Jajcus/midi_touch_keyboard/src/touch_sensors.rs

use defmt::{debug, info, write, Format, Formatter};

use embassy_rp::gpio::{Flex, Pull};
use embassy_time::{Duration, Instant, Timer};

use crate::config::*;

#[derive(Default, Clone, Copy, Format, PartialEq)]
pub enum CalibrationStatus {
    #[default]
    NA,
    Ok,
    Bad,
}

#[derive(Clone, Copy)]
pub struct CalibrationData {
    pub min_time: Duration,
    pub max_time: Duration,
    pub status: CalibrationStatus,
}

impl Default for CalibrationData {
    fn default() -> Self {
        Self {
            min_time: Duration::MAX,
            max_time: Duration::MIN,
            status: CalibrationStatus::NA,
        }
    }
}

#[derive(Default, Clone, Copy)]
pub struct CalibrationDataSet {
    pub pins: [CalibrationData; NUM_SENSORS],
    pub all: CalibrationData,
    pub status: CalibrationStatus,
}

impl Format for CalibrationDataSet {
    fn format(&self, f: Formatter) {
        write!(f, "{}: ", self.status);
        let mut first = true;
        for pin_data in self.pins {
            if !first {
                write!(f, ", ");
            } else {
                first = false;
            }
            write!(f, "{}[", pin_data.status);
            if pin_data.min_time < Duration::MAX {
                write!(f, "{}", pin_data.min_time.as_micros());
            }
            write!(f, "..");
            if pin_data.max_time > Duration::MIN {
                write!(f, "{}", pin_data.max_time.as_micros());
            }
            write!(f, "]");
        }
    }
}

#[derive(Default, Clone, Copy, Format, PartialEq)]
pub enum TouchSensorStatus {
    #[default]
    NA,
    On,
    Off,
}

pub struct TouchSensors<'a> {
    pins: [Flex<'a>; NUM_SENSORS],
    calibration: CalibrationDataSet,
    threshold: Duration,
}

impl<'a> TouchSensors<'a> {
    pub fn new(mut pins: [Flex<'a>; NUM_SENSORS]) -> Self {
        let threshold = Duration::from_micros(500);

        for pin in &mut pins {
            pin.set_pull(Pull::None);
        }

        Self {
            pins,
            calibration: Default::default(),
            threshold,
        }
    }
    pub async fn calibrate_start(&mut self) {
        info!("Calibration start");
        self.calibration = Default::default();
    }
    pub async fn calibrate_step(&mut self) -> CalibrationDataSet {
        info!("Calibration step");

        for pin in &mut self.pins {
            pin.set_as_output();
            pin.set_high();
        }

        Timer::after(Duration::from_micros(1)).await;

        let t0 = Instant::now();

        for pin in &mut self.pins {
            pin.set_as_input();
        }

        let mut already_done: [bool; NUM_SENSORS] = [false; NUM_SENSORS];
        let mut num_done = 0;
        let all_c = &mut self.calibration.all;
        loop {
            Timer::after(Duration::from_micros(1)).await;
            let t = Instant::elapsed(&t0);
            let done: [bool; NUM_SENSORS] = core::array::from_fn(|i| self.pins[i].is_low());

            for i in 0..NUM_SENSORS {
                if already_done[i] {
                    continue;
                }
                if done[i] {
                    let pin_c = &mut self.calibration.pins[i];
                    if t < pin_c.min_time {
                        pin_c.min_time = t;
                    }
                    if t > pin_c.max_time {
                        pin_c.max_time = t;
                    }
                    if pin_c.min_time < MIN_TIME_REQUIRED {
                        pin_c.status = CalibrationStatus::Bad;
                    } else if pin_c.max_time - pin_c.min_time >= MIN_MARGIN_REQUIRED {
                        pin_c.status = CalibrationStatus::Ok;

                        // get those only from reasonable-behaving pins
                        if pin_c.min_time < all_c.min_time {
                            all_c.min_time = t;
                        }
                        if pin_c.max_time > all_c.max_time {
                            all_c.max_time = t;
                        }
                    }
                    already_done[i] = true;
                    num_done += 1;
                }
            }

            if all_c.max_time > all_c.min_time {
                // we have some usable data, use it to find some bad sensors
                for i in 0..NUM_SENSORS {
                    let pin_c = &mut self.calibration.pins[i];
                    if pin_c.min_time > all_c.max_time {
                        pin_c.status = CalibrationStatus::Bad;
                    }
                }
            }

            if num_done == NUM_SENSORS || t >= CALIBRATION_STEP_TIME {
                break;
            };
        }

        self.calibration
    }
    pub async fn calibrate_stop(&mut self) -> CalibrationDataSet {
        info!("Calibration end");
        let max_min = self
            .calibration
            .pins
            .iter()
            .filter(|x| x.status == CalibrationStatus::Ok)
            .map(|x| x.min_time)
            .max();
        let min_max = self
            .calibration
            .pins
            .iter()
            .filter(|x| x.status == CalibrationStatus::Ok)
            .map(|x| x.max_time)
            .min();

        match (max_min, min_max) {
            (Some(max_min), Some(min_max)) => {
                if min_max < max_min || (min_max - max_min) < MIN_MARGIN_REQUIRED / 10 {
                    info!(
                        "Bad calibration max min: {}  min max: {}",
                        max_min.as_micros(),
                        min_max.as_micros()
                    );
                } else {
                    self.calibration.all.min_time = max_min;
                    self.calibration.all.max_time = min_max;
                };
                self.threshold = self.calibration.all.min_time + self.calibration.all.max_time / 2;
                self.calibration.status = CalibrationStatus::Ok;
            }
            (_, _) => {
                info!("Bad calibration no single good pin");
                self.threshold = CALIBRATION_STEP_TIME / 2;
                self.calibration.status = CalibrationStatus::Bad;
            }
        }
        info!(
            "status: {}, threshold: {}",
            self.calibration.status,
            self.threshold.as_micros()
        );
        self.calibration.all.status = self.calibration.status;
        self.calibration
    }
    pub fn set_sensitivity(&mut self, permile: u32) {
        let range = self.calibration.all.max_time - self.calibration.all.min_time;
        self.threshold = self.calibration.all.min_time + range * (1000 - permile) / 1000;
    }
    pub async fn take_sample(&mut self) -> [TouchSensorStatus; NUM_SENSORS] {
        for pin in &mut self.pins {
            pin.set_as_output();
            pin.set_high();
        }

        Timer::after(Duration::from_micros(1)).await;

        let t0 = Instant::now();

        for pin in &mut self.pins {
            pin.set_as_input();
        }

        Timer::at(t0 + self.threshold).await;
        let on: [bool; NUM_SENSORS] = core::array::from_fn(|i| self.pins[i].is_high());

        core::array::from_fn(|i| match (self.calibration.pins[i].status, on[i]) {
            (CalibrationStatus::Ok, true) => TouchSensorStatus::On,
            (CalibrationStatus::NA, true) => TouchSensorStatus::On,
            (CalibrationStatus::Ok, false) => TouchSensorStatus::Off,
            (CalibrationStatus::NA, false) => TouchSensorStatus::Off,
            (CalibrationStatus::Bad, _) => TouchSensorStatus::NA,
        })
    }
    pub async fn run(&mut self) -> [TouchSensorStatus; NUM_SENSORS] {
        let mut result = self.take_sample().await;
        debug!("sample: {}", result);
        for _i in 0..(SENSOR_SAMPLES - 1) {
            let new_sample = self.take_sample().await;
            debug!("sample: {}", new_sample);
            for (fin, cur) in result.iter_mut().zip(new_sample.iter()) {
                if *fin != *cur {
                    *fin = TouchSensorStatus::NA;
                }
            }
        }
        result
    }
}
