Jajcus/midi_touch_keyboard/src/config.rs

use embassy_time::Duration;

// constants used throughout the code

// sensors
pub const NUM_SENSORS: usize = 16;
pub const SENSOR_SAMPLES: usize = 10;
pub const CALIBRATION_STEP_TIME: Duration = Duration::from_micros(5000);
pub const MIN_TIME_REQUIRED: Duration = Duration::from_micros(10);
pub const MIN_MARGIN_REQUIRED: Duration = Duration::from_micros(100);

// leds
pub const NUM_LEDS: usize = 19;
pub const WELCOME_COLORS: [u32; NUM_LEDS] = [
    0x80000, 0x008000, 0x000080, 0x40000, 0x004000, 0x000040, 0x20000, 0x002000, 0x000020, 0x80000,
    0x008000, 0x000080, 0x40000, 0x004000, 0x000040, 0x20000, 0x002000, 0x000020, 0x10000,
];

pub const COL_WHITE_OFF: u32 = 0x020202;
pub const COL_WHITE_ON: u32 = 0x101010;
pub const COL_BLACK_OFF: u32 = 0x000101;
pub const COL_BLACK_ON: u32 = 0x00808;
pub const COL_BROKEN: u32 = 0x010000;
pub const COL_UNUSED: u32 = 0x000000;

#[derive(Clone, Copy)]
pub enum PianoKey {
    White,
    Black,

    #[allow(dead_code)]
    Missing,
}

// must be still valid (just brighter) when multiplied by 4
pub const COL_CAL_NA: u32 = 0x020100;
pub const COL_CAL_OK: u32 = 0x000200;
pub const COL_CAL_BAD: u32 = 0x040000;

pub const SENSOR_TO_LED: [Option<usize>; NUM_SENSORS] = [
    Some(9),
    Some(8),
    Some(11),
    Some(7),
    Some(12),
    Some(6),
    Some(5),
    Some(14),
    Some(4),
    Some(15),
    Some(3),
    Some(16),
    Some(2),
    Some(1),
    Some(18),
    Some(0),
];

pub const ROOT_NOTE: i8 = 60;

// mapping of sensors to MIDI notes (MIDI number of the root note will be added)
pub const SENSOR_TO_NOTE: [Option<i8>; NUM_SENSORS] = [
    Some(-1), // B
    Some(0),  // C
    Some(1),  // C#
    Some(2),  // D
    Some(3),  // D#
    Some(4),  // E
    Some(5),  // F
    Some(6),  // F#
    Some(7),  // G
    Some(8),  // G#
    Some(9),  // A
    Some(10), // A#
    Some(11), // B
    Some(12), // C
    Some(13), // C#
    Some(14), // D
];

// mapping of sensors to piano key colors
pub const SENSOR_TO_PIANO_KEY: [PianoKey; NUM_SENSORS] = [
    PianoKey::White, // B
    PianoKey::White, // C
    PianoKey::Black, // C#
    PianoKey::White, // D
    PianoKey::Black, // D#
    PianoKey::White, // E
    PianoKey::White, // F
    PianoKey::Black, // F#
    PianoKey::White, // G
    PianoKey::Black, // G#
    PianoKey::White, // A
    PianoKey::Black, // A#
    PianoKey::White, // B
    PianoKey::White, // C
    PianoKey::Black, // C#
    PianoKey::White, // D
];

// button
pub const DEBOUNCE_TIME: Duration = Duration::from_millis(2);

// adc
pub const ADC_INTERVAL: Duration = Duration::from_millis(10);

// MIDI
// let it hold note-offs for all keys and a few more messages
pub const MIDI_CHANNEL_SIZE: usize = 20;

// serial MIDI
pub const SERIAL_MIDI_BUF_LEN: usize = 128;
