Jajcus/midi_touch_keyboard/src/lib.rs

#![no_std]

// for other binaries (test tools)

pub mod adc;
pub mod board;
pub mod button;
pub mod config;
pub mod midi;
pub mod serial_midi;
pub mod touch_sensors;
pub mod usb_midi;
pub mod ws2812b;
